sonic-insurgence/Cookie-Synthesizer/documentation/images/Workshop Cookie Mockup1.jpg

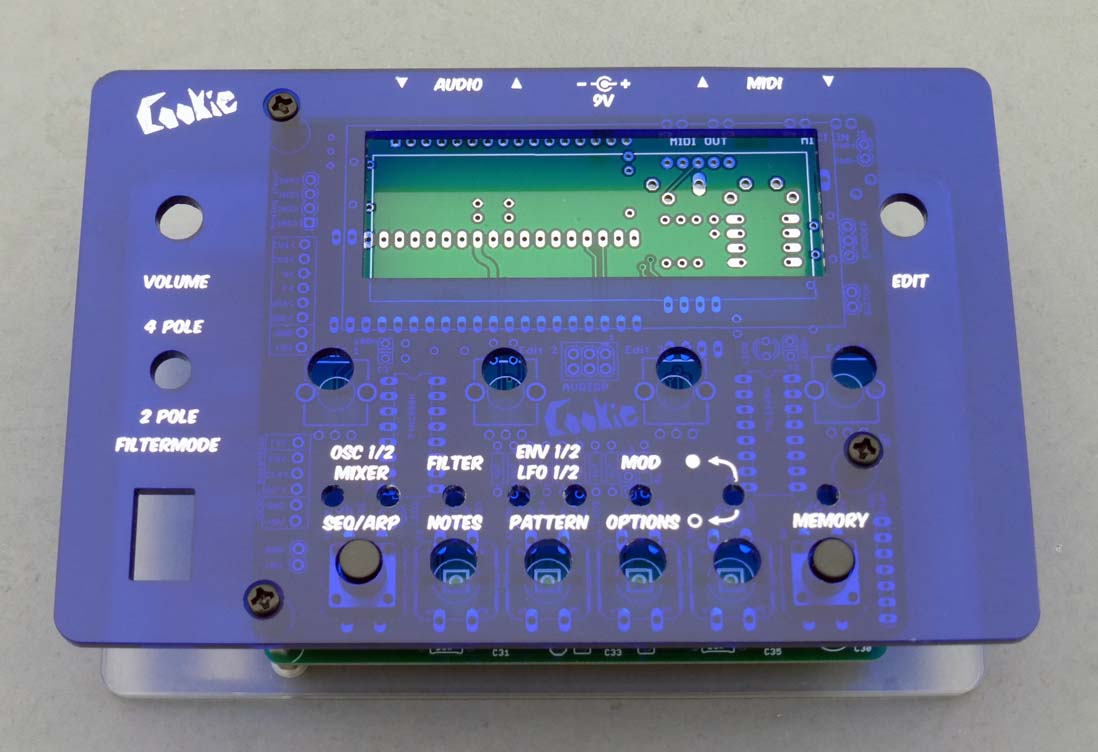
documentation/images/Workshop Cookie Mockup1.jpg
