sonic-insurgence/Cookie-Synthesizer/documentation/images/Workshop Cookie Mockup3.jpg

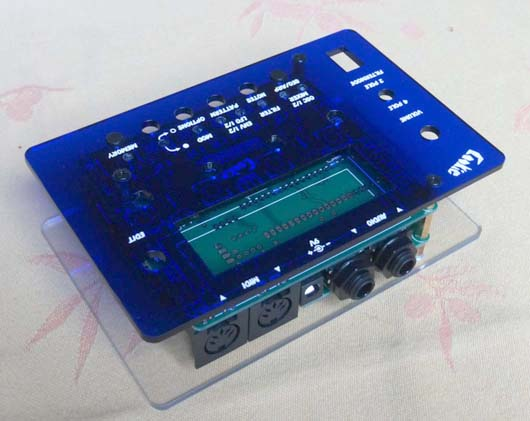
documentation/images/Workshop Cookie Mockup3.jpg
