sonic-insurgence/Cookie-Synthesizer/documentation/images/Workshop Cookie Neon1.jpg

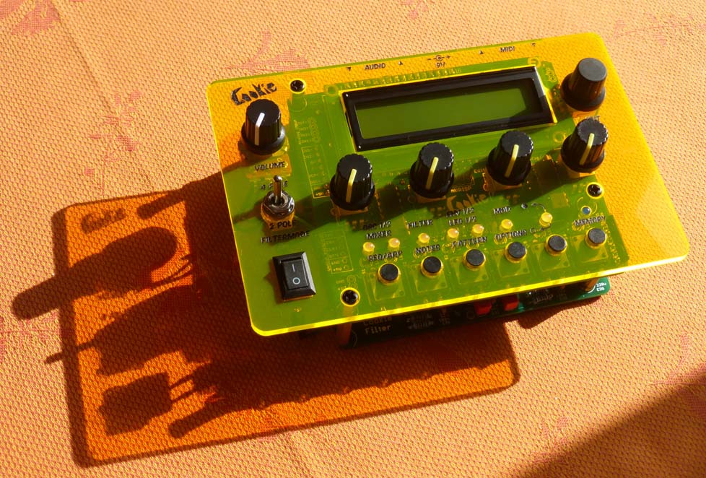
documentation/images/Workshop Cookie Neon1.jpg
