sonic-insurgence/Cookie-Synthesizer/documentation/images/Workshop kit.jpg

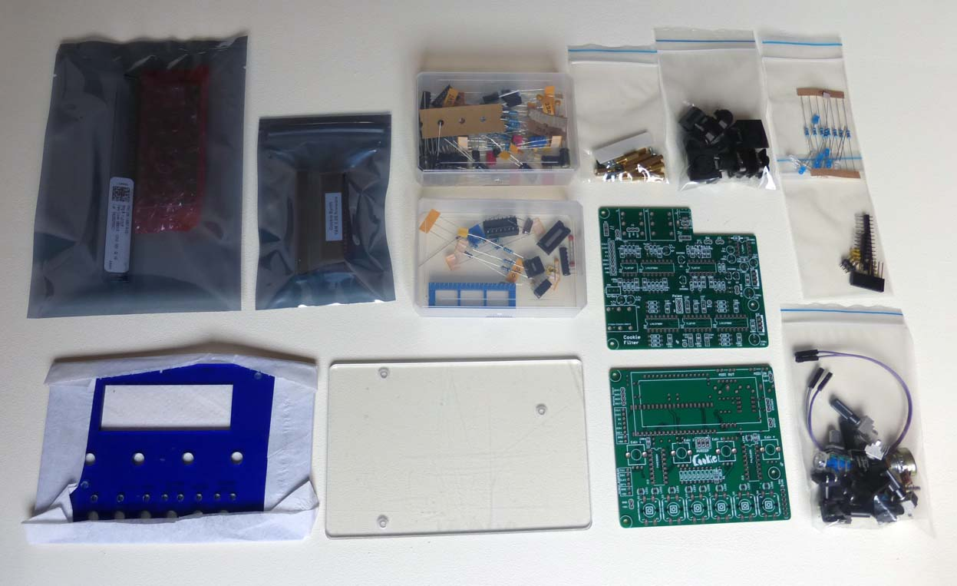
documentation/images/Workshop kit.jpg
